CyberSaiyanIT/rhc22-badge/main/badge/common/storage.c

#include "storage.h"

void nvs_init()
{
    esp_err_t ret = nvs_flash_init();
    if (ret == ESP_ERR_NVS_NO_FREE_PAGES || ret == ESP_ERR_NVS_NEW_VERSION_FOUND) {
        ESP_ERROR_CHECK(nvs_flash_erase());
        ret = nvs_flash_init();
    }
    ESP_ERROR_CHECK(ret);
}

void spiffs_init()
{
    esp_vfs_spiffs_conf_t conf = {
      .base_path = "/data",
      .partition_label = NULL,
      .max_files = 20,
      .format_if_mount_failed = false
    };

    // Use settings defined above to initialize and mount SPIFFS filesystem.
    // Note: esp_vfs_spiffs_register is an all-in-one convenience function.
    esp_err_t ret = esp_vfs_spiffs_register(&conf);
    
    if (ret != ESP_OK) {
        if (ret == ESP_FAIL) {
            ESP_LOGE(__FILE__, "Failed to mount or format filesystem");
        } else if (ret == ESP_ERR_NOT_FOUND) {
            ESP_LOGE(__FILE__, "Failed to find SPIFFS partition");
        } else {
            ESP_LOGE(__FILE__, "Failed to initialize SPIFFS (%s)", esp_err_to_name(ret));
        }
        return;
    }
    
    size_t total = 0, used = 0;
    ret = esp_spiffs_info(conf.partition_label, &total, &used);
    if (ret != ESP_OK) {
        ESP_LOGE(__FILE__, "Failed to get SPIFFS partition information (%s)", esp_err_to_name(ret));
    } else {
        ESP_LOGI(__FILE__, "Partition size: total: %d, used: %d", total, used);
    }
}
