CyberSaiyanIT/rhc22-badge/main/badge/httpd.h

#ifndef __HTTPD_H
#define __HTTPD_H
#include <stdio.h>
#include <stdlib.h>
#include <string.h>
#include <string.h>
#include <fcntl.h>
#include "esp_http_server.h"
#include "esp_system.h"
#include "esp_log.h"
#include "esp_vfs.h"
#include "cJSON.h"

#include "badge.h"

#define REST_CHECK(a, str, goto_tag, ...)                                              \
    do                                                                                 \
    {                                                                                  \
        if (!(a))                                                                      \
        {                                                                              \
            ESP_LOGE(REST_TAG, "%s(%d): " str, __FUNCTION__, __LINE__, ##__VA_ARGS__); \
            goto goto_tag;                                                             \
        }                                                                              \
    } while (0)

#define FILE_PATH_MAX (ESP_VFS_PATH_MAX + 128)
#define SCRATCH_BUFSIZE (2048)
#define BASE_PATH "/data/www"
#define API_ENDPOINT "/api/v1/"
#define API_ENDPOINT_WILDCARD "/api/v1/*"

typedef struct rest_server_context {
    char base_path[ESP_VFS_PATH_MAX + 1];
    char scratch[SCRATCH_BUFSIZE];
} rest_server_context_t;

#define SESSION_KEY_LEN 8

void disconnect_handler(void* arg, esp_event_base_t event_base,
                               int32_t event_id, void* event_data);

void connect_handler(void* arg, esp_event_base_t event_base,
                               int32_t event_id, void* event_data);
#endif
